markdhooper/rfgrid-ECED4900/applications/RPG/images/objects/dead.png

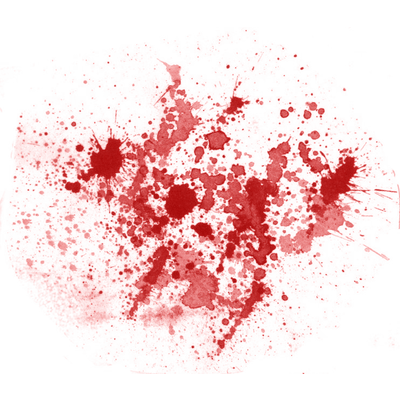
applications/RPG/images/objects/dead.png
