markdhooper/rfgrid-ECED4900/applications/RPG/images/objects/e1.png

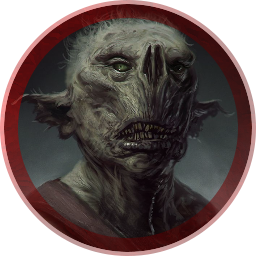
applications/RPG/images/objects/e1.png
