markdhooper/rfgrid-ECED4900/applications/RPG/images/objects/e2.png

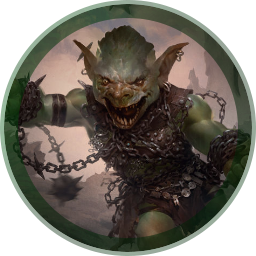
applications/RPG/images/objects/e2.png
