markdhooper/rfgrid-ECED4900/applications/RPG/images/objects/e3.png

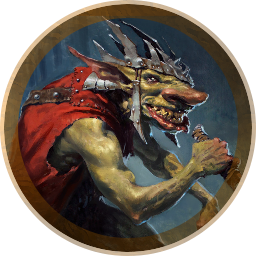
applications/RPG/images/objects/e3.png
