markdhooper/rfgrid-ECED4900/applications/RPG/images/objects/e5.png

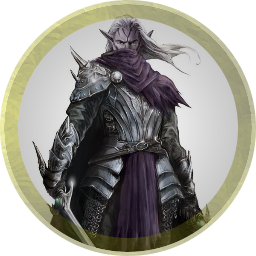
applications/RPG/images/objects/e5.png
