markdhooper/rfgrid-ECED4900/applications/RPG/images/objects/mindFlayer.png

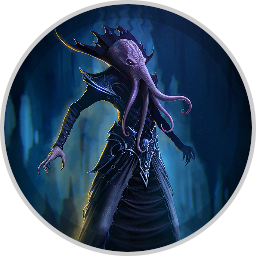
applications/RPG/images/objects/mindFlayer.png
