markdhooper/rfgrid-ECED4900/applications/RPG/images/objects/wizard.png

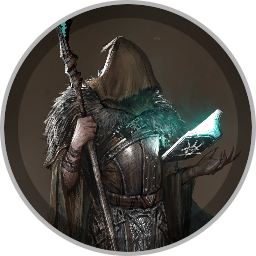
applications/RPG/images/objects/wizard.png
