markdhooper/rfgrid-ECED4900/applications/rpg_non_communicating/images/objects/paladin.png

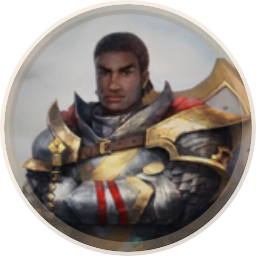
applications/rpg_non_communicating/images/objects/paladin.png
