markdhooper/rfgrid-ECED4900/applications/sequencer/images/objects/b1.png

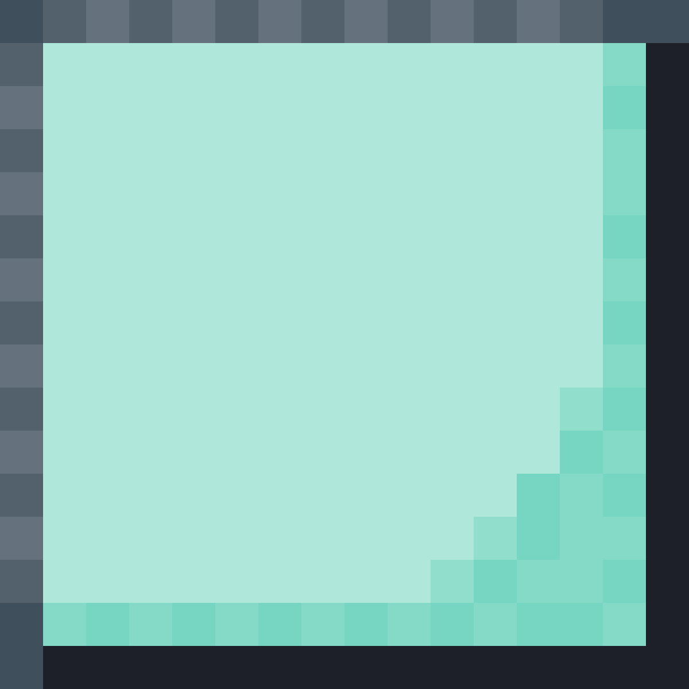
applications/sequencer/images/objects/b1.png
