markdhooper/rfgrid-ECED4900/applications/sequencer/images/objects/bpm100.png

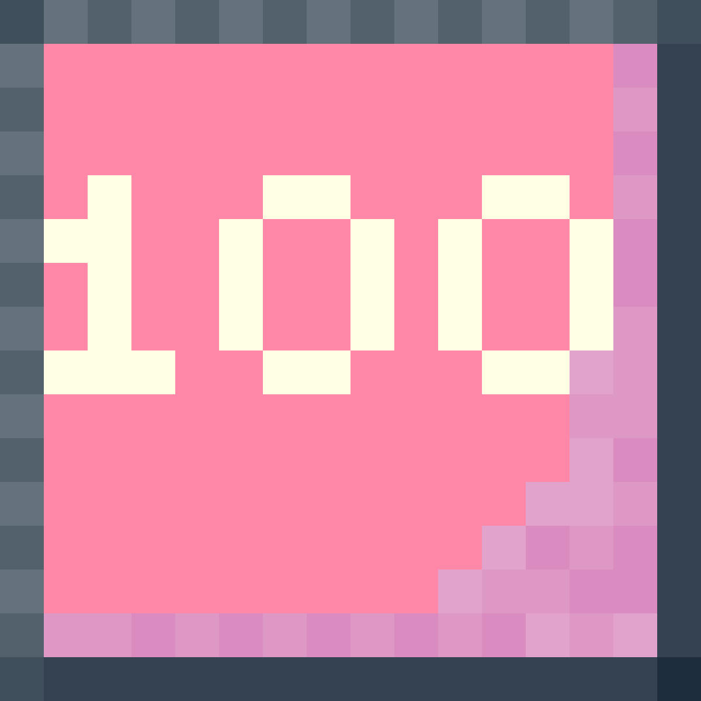
applications/sequencer/images/objects/bpm100.png
