markdhooper/rfgrid-ECED4900/applications/sequencer/images/objects/cb1.png

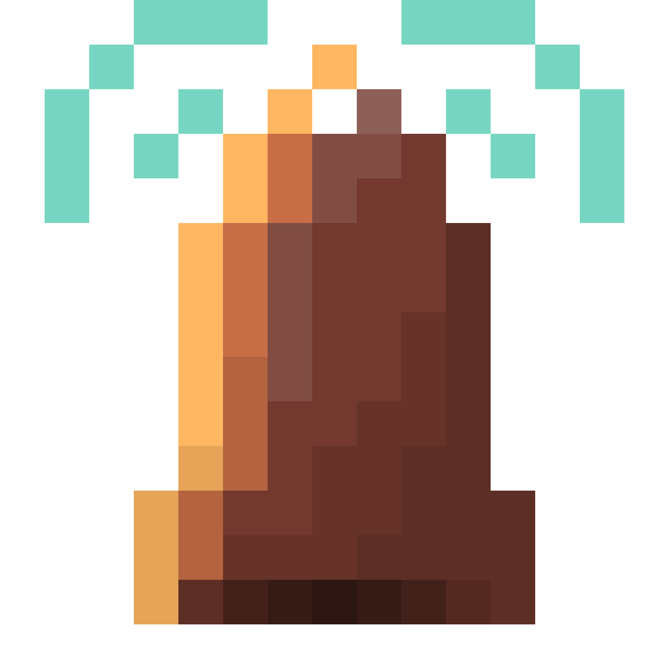
applications/sequencer/images/objects/cb1.png
