markdhooper/rfgrid-ECED4900/applications/sequencer/images/objects/chh1.png

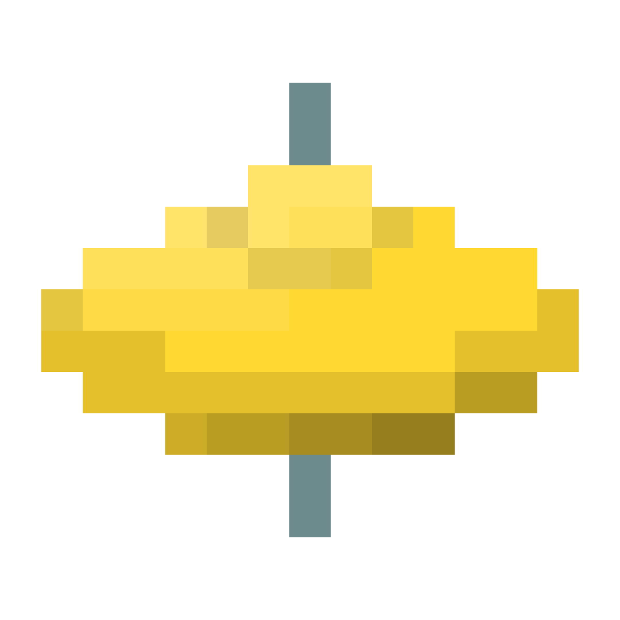
applications/sequencer/images/objects/chh1.png
