markdhooper/rfgrid-ECED4900/applications/sequencer/images/objects/cl1.png

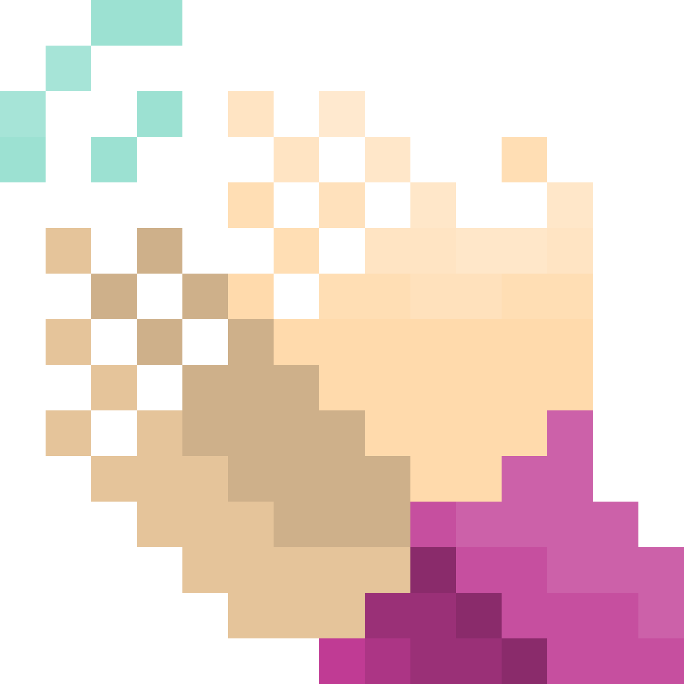
applications/sequencer/images/objects/cl1.png
