markdhooper/rfgrid-ECED4900/applications/sequencer/images/objects/cr1.png

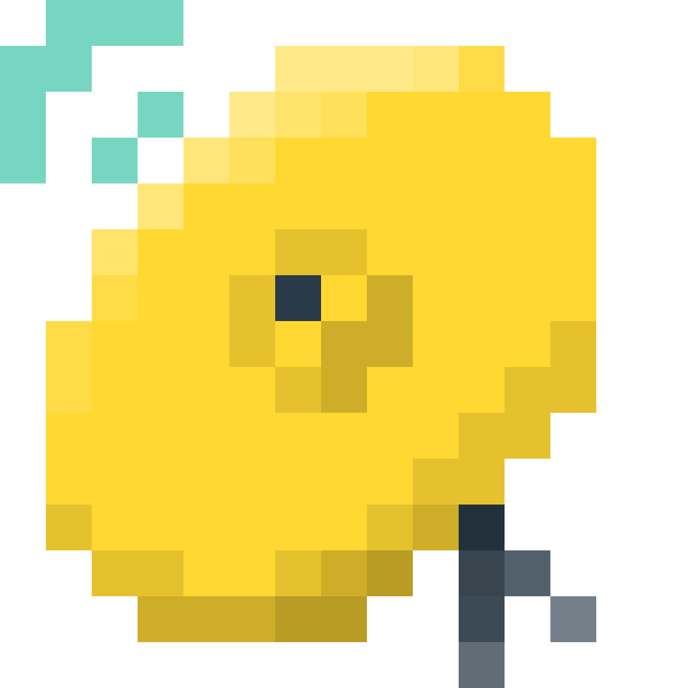
applications/sequencer/images/objects/cr1.png
