markdhooper/rfgrid-ECED4900/applications/sequencer/images/objects/cr2.png

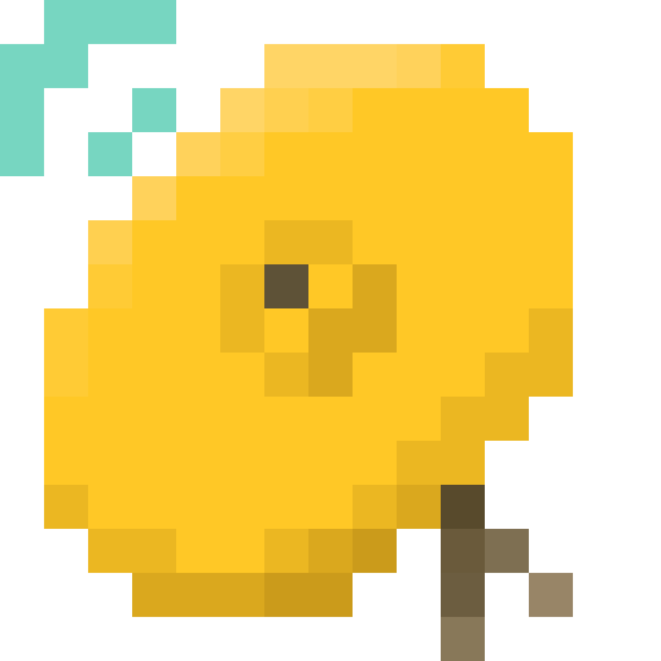
applications/sequencer/images/objects/cr2.png
