markdhooper/rfgrid-ECED4900/applications/sequencer/images/objects/k1.png

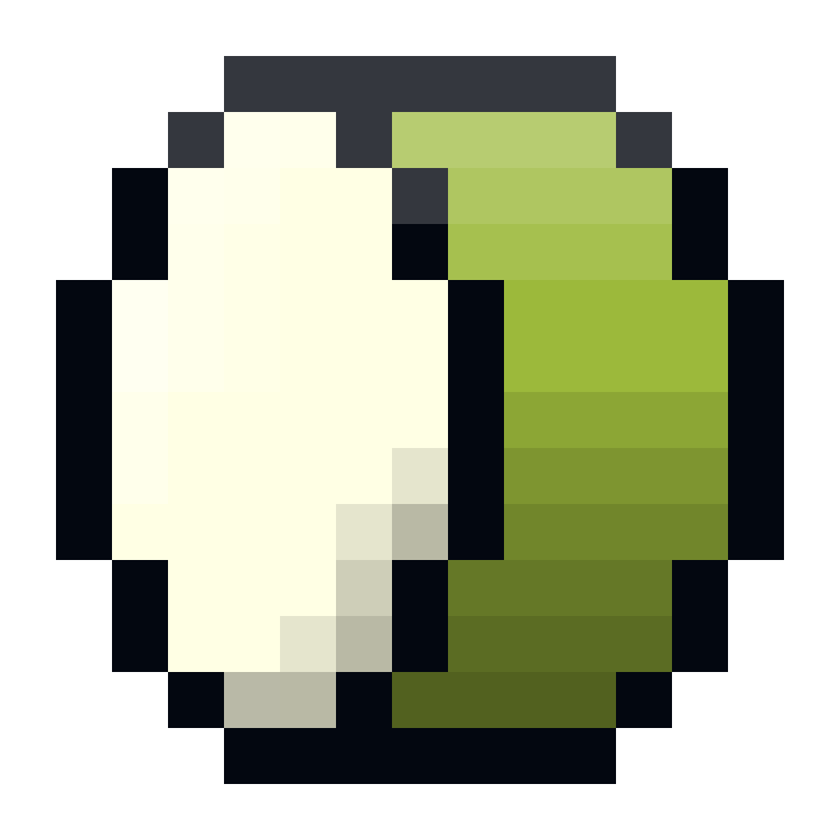
applications/sequencer/images/objects/k1.png
