markdhooper/rfgrid-ECED4900/applications/sequencer/images/objects/load.png

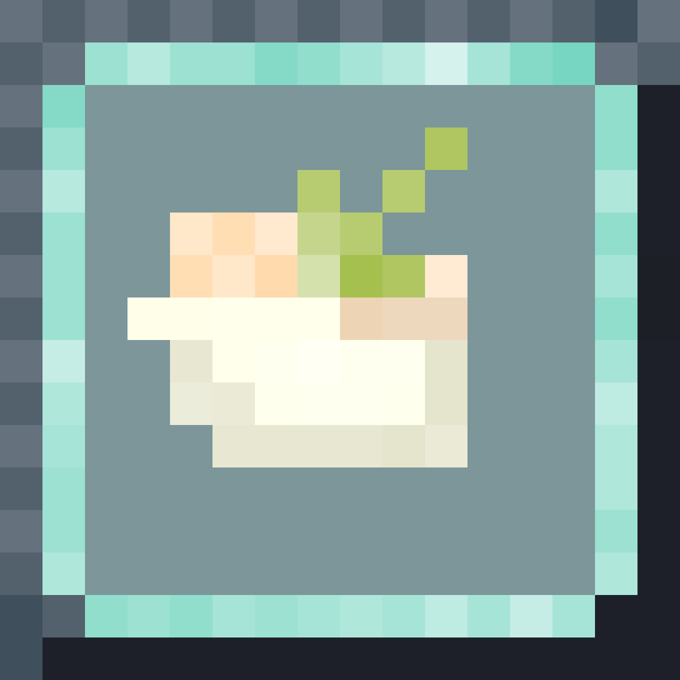
applications/sequencer/images/objects/load.png
