markdhooper/rfgrid-ECED4900/applications/sequencer/images/objects/m1.png

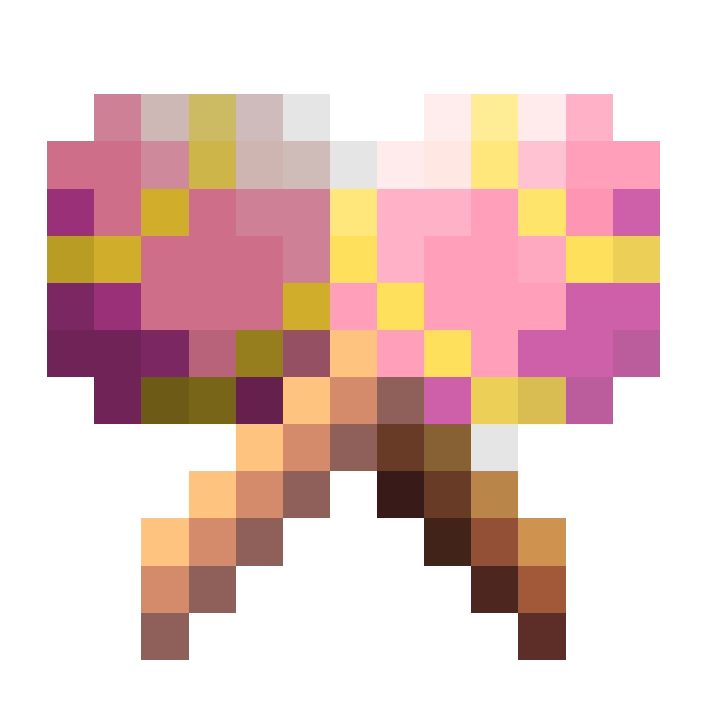
applications/sequencer/images/objects/m1.png
