markdhooper/rfgrid-ECED4900/applications/sequencer/images/objects/ohh1.png

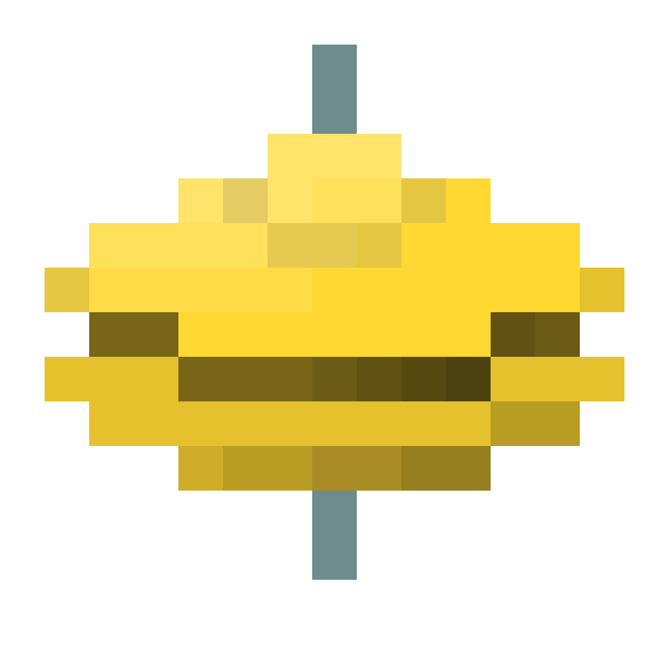
applications/sequencer/images/objects/ohh1.png
