markdhooper/rfgrid-ECED4900/applications/sequencer/images/objects/pause.png

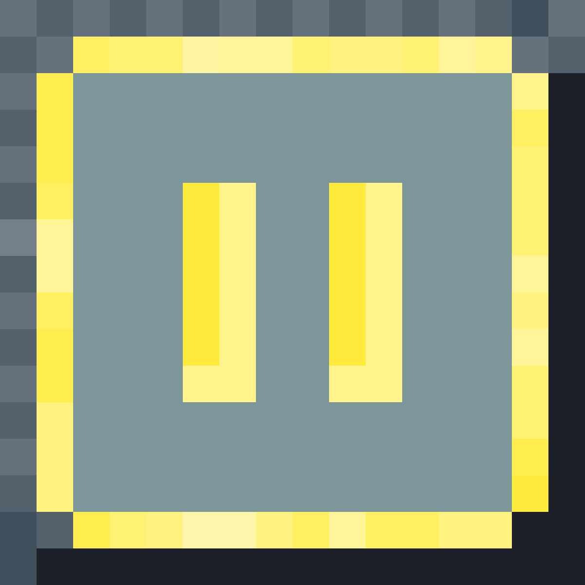
applications/sequencer/images/objects/pause.png
