markdhooper/rfgrid-ECED4900/applications/sequencer/images/objects/play.png

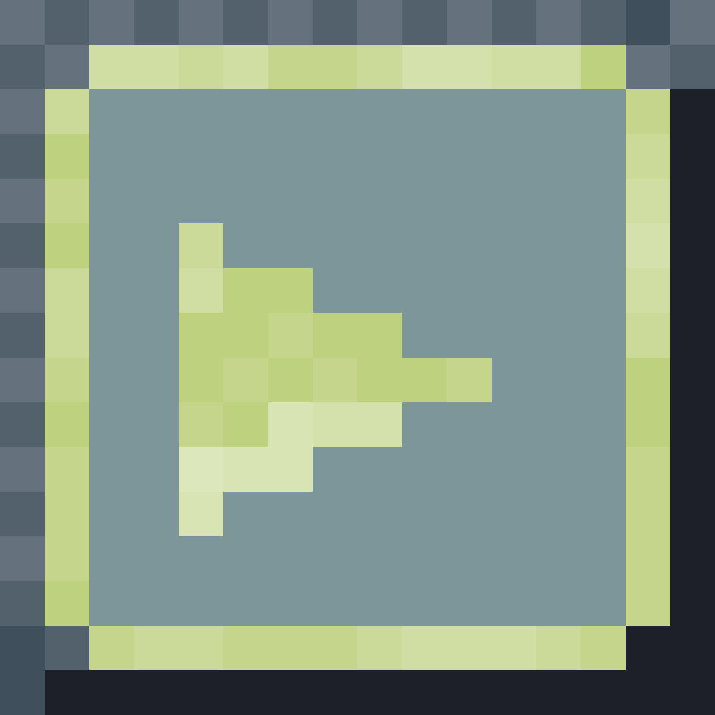
applications/sequencer/images/objects/play.png
