markdhooper/rfgrid-ECED4900/applications/sequencer/images/objects/rec.png

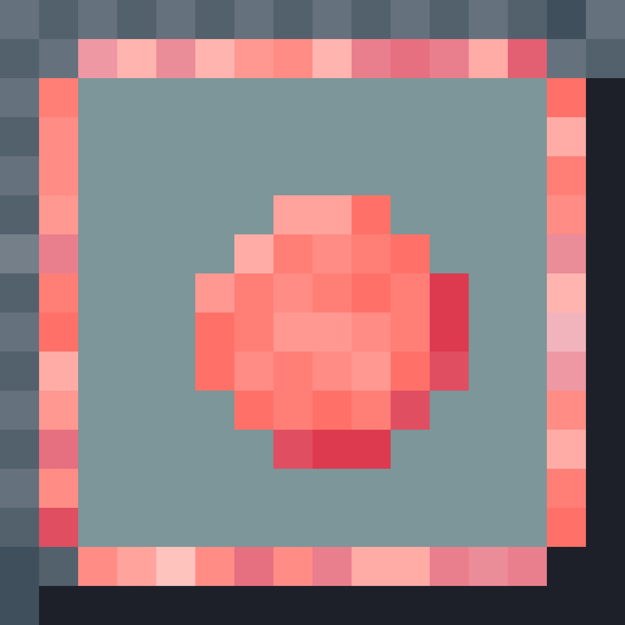
applications/sequencer/images/objects/rec.png
