markdhooper/rfgrid-ECED4900/applications/sequencer/images/objects/sn1.png

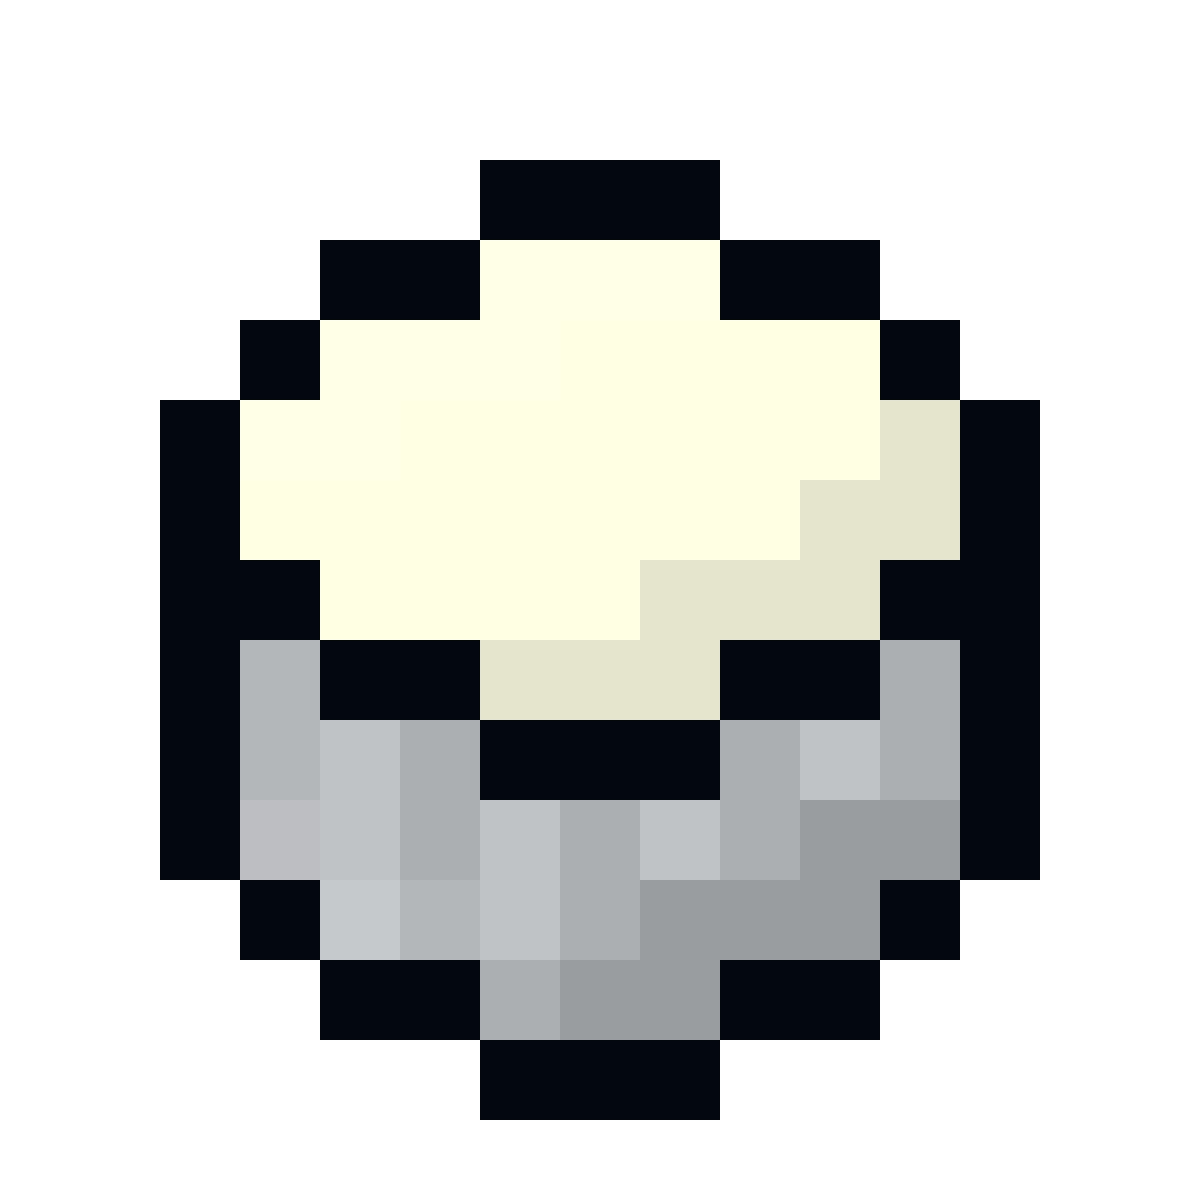
applications/sequencer/images/objects/sn1.png
