markdhooper/rfgrid-ECED4900/applications/sequencer/images/objects/t1.png

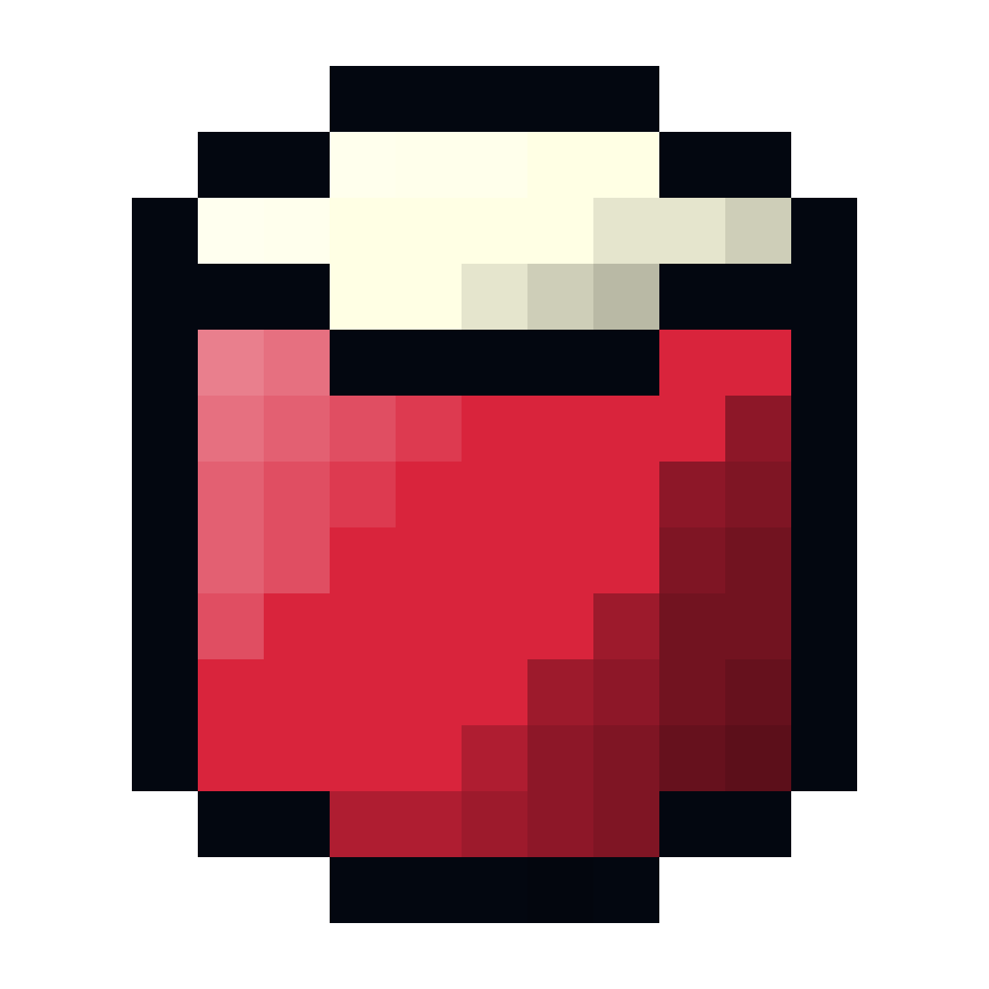
applications/sequencer/images/objects/t1.png
