markdhooper/rfgrid-ECED4900/applications/sequencer/images/objects/v1.png

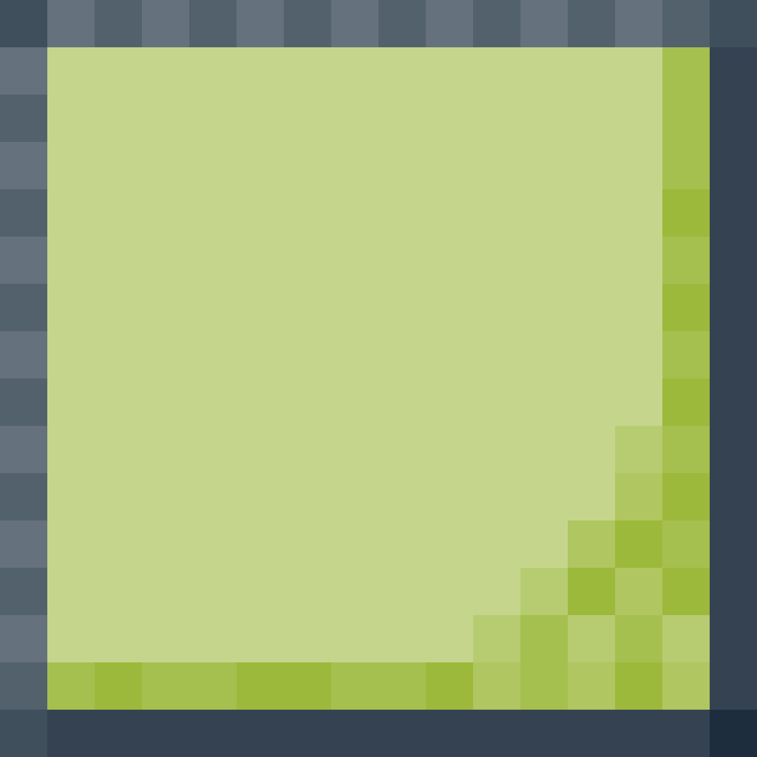
applications/sequencer/images/objects/v1.png
