markdhooper/rfgrid-ECED4900/docs/photos/solidWorksRender.jpg

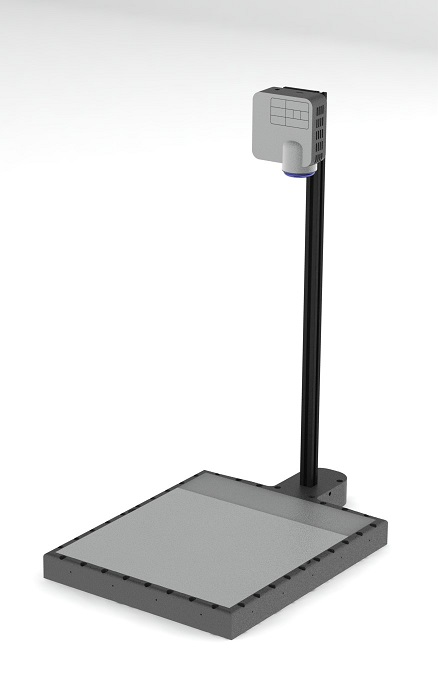
docs/photos/solidWorksRender.jpg
