markdhooper/rfgrid-ECED4900/RFGrid-GUI/RFGrid GUI/Resources/mage.png

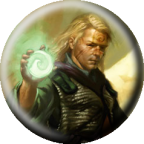
RFGrid-GUI/RFGrid GUI/Resources/mage.png
