markdhooper/rfgrid-ECED4900/docs/cadModels/SolidWorks/projection_surface.SLDPRT

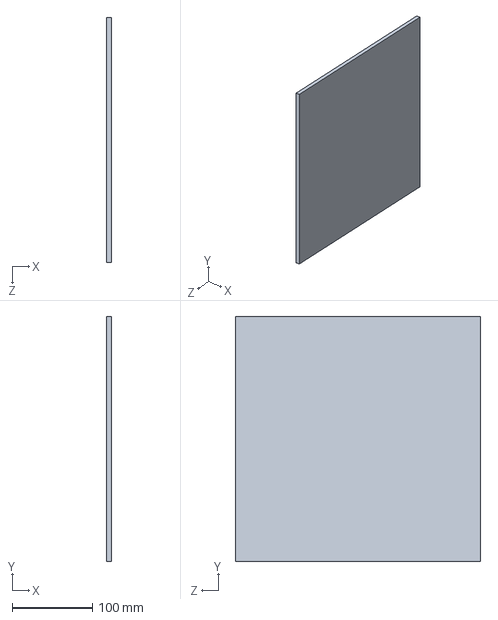
[picture p51: CAD file, 2020-02-15]
docs/cadModels/SolidWorks/projection_surface.SLDPRT
6.35 x 304.8 x 304.8 mm
