markdhooper/rfgrid-ECED4900/docs/cadModels/SolidWorks/menu_surface.SLDPRT

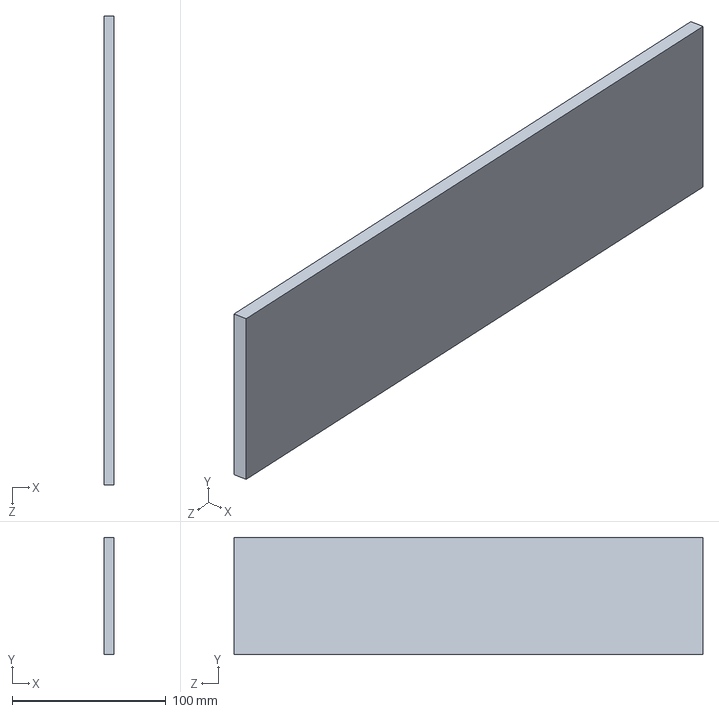
[picture p52: CAD file, 2020-02-15]
docs/cadModels/SolidWorks/menu_surface.SLDPRT
6.35 x 76.2 x 304.8 mm
