markdhooper/rfgrid-ECED4900/docs/cadModels/SolidWorks/extruded_aluminium_a.SLDPRT

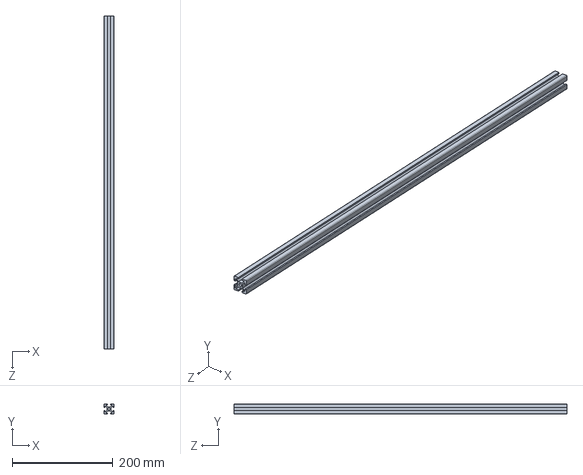
[picture p53: CAD file, 2020-02-15]
docs/cadModels/SolidWorks/extruded_aluminium_a.SLDPRT
20.0 x 20.0 x 660.4 mm
