markdhooper/rfgrid-ECED4900/docs/cadModels/SolidWorks/reader_tray.SLDPRT

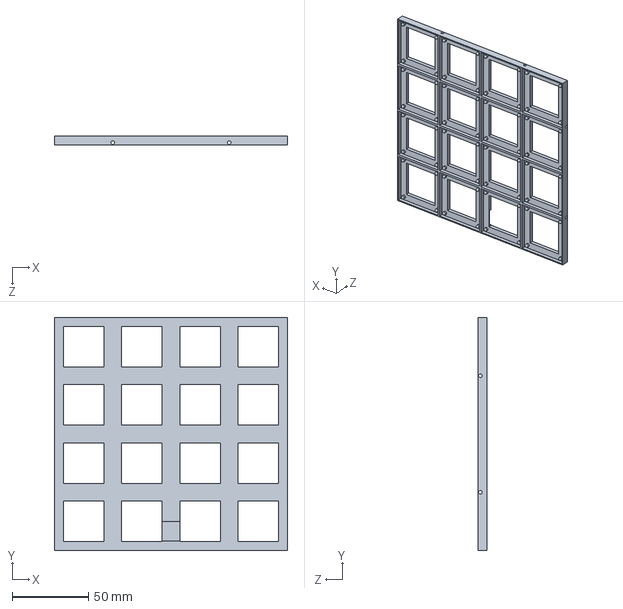
[picture p54: CAD file, 2020-02-15]
docs/cadModels/SolidWorks/reader_tray.SLDPRT
152.4 x 152.4 x 5.59 mm
